CITCEuraRFID/KeyDuino/KeyDuino/mac_link.cpp

#include "mac_link.h"
#include "KeyDuino_debug.h"

int8_t MACLink::activateAsTarget(uint16_t timeout)
{
    keyduino.begin();
    keyduino.SAMConfig();
    return keyduino.tgInitAsTarget(timeout);
}

bool MACLink::write(const uint8_t *header, uint8_t hlen, const uint8_t *body, uint8_t blen)
{
    return keyduino.tgSetData(header, hlen, body, blen);
}

int16_t MACLink::read(uint8_t *buf, uint8_t len)
{
    return keyduino.tgGetData(buf, len);
}
