CITCEuraRFID/KeyDuino/KeyDuinoESP/ESP/Utils.ino

/********** Utils functions **********/

char* strToChar(String s) {
  unsigned int bufSize = s.length() + 1; //String length + null terminator
  char* ret = new char[bufSize];
  s.toCharArray(ret, bufSize);
  return ret;
}

String macToStr(const uint8_t* mac) {
  String result;
  for (int i = 0; i < 6; ++i) {
    result += String(mac[i], 16);
    //if (i < 5)
    //result += ':';
  }
  return result;
}
